Ehryk/GearDisplay/Documentation/PCB Routing/Shift Sensor Unit - v4.png

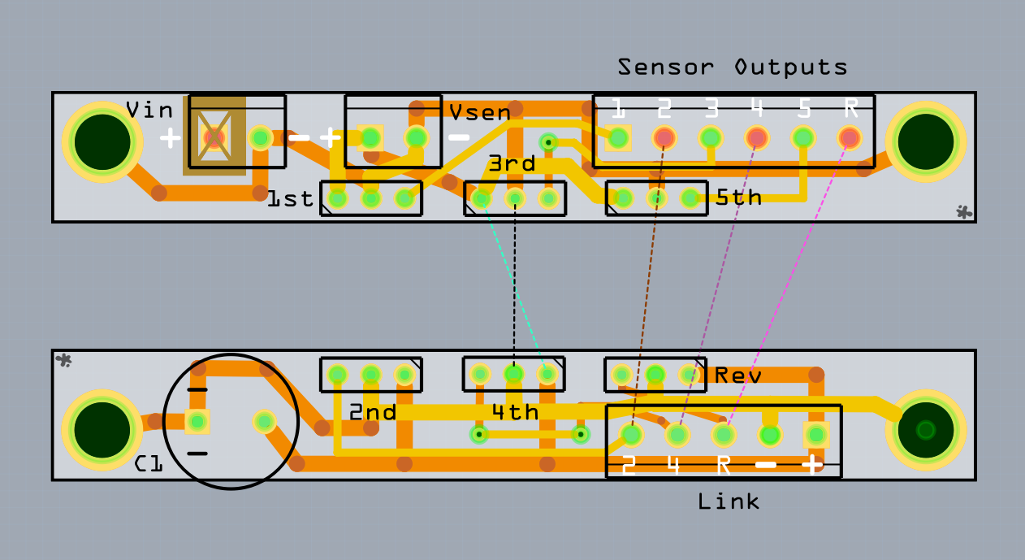
Documentation/PCB Routing/Shift Sensor Unit - v4.png
