Ehryk/GearDisplay/Documentation/Pictures/2013.01.10 - Breadboard/2 - Intro Credits.jpg

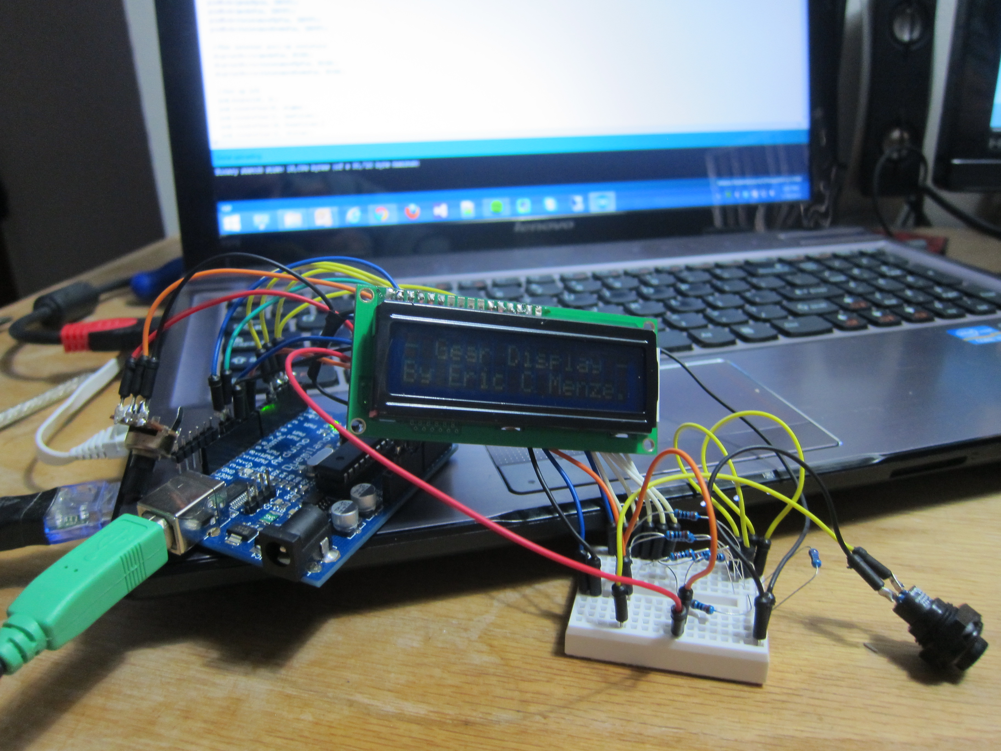
Documentation/Pictures/2013.01.10 - Breadboard/2 - Intro Credits.jpg
