Ehryk/GearDisplay/Documentation/Pictures/2013.01.10 - Breadboard/3 - Second Gear.jpg

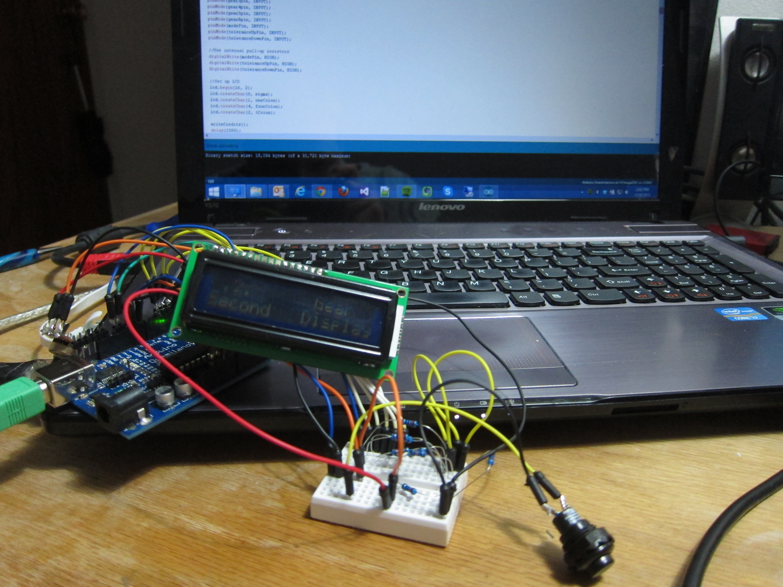
Documentation/Pictures/2013.01.10 - Breadboard/3 - Second Gear.jpg
