Ehryk/GearDisplay/Documentation/Pictures/2013.01.20 - Stripboard/1 - Basic Display.jpg

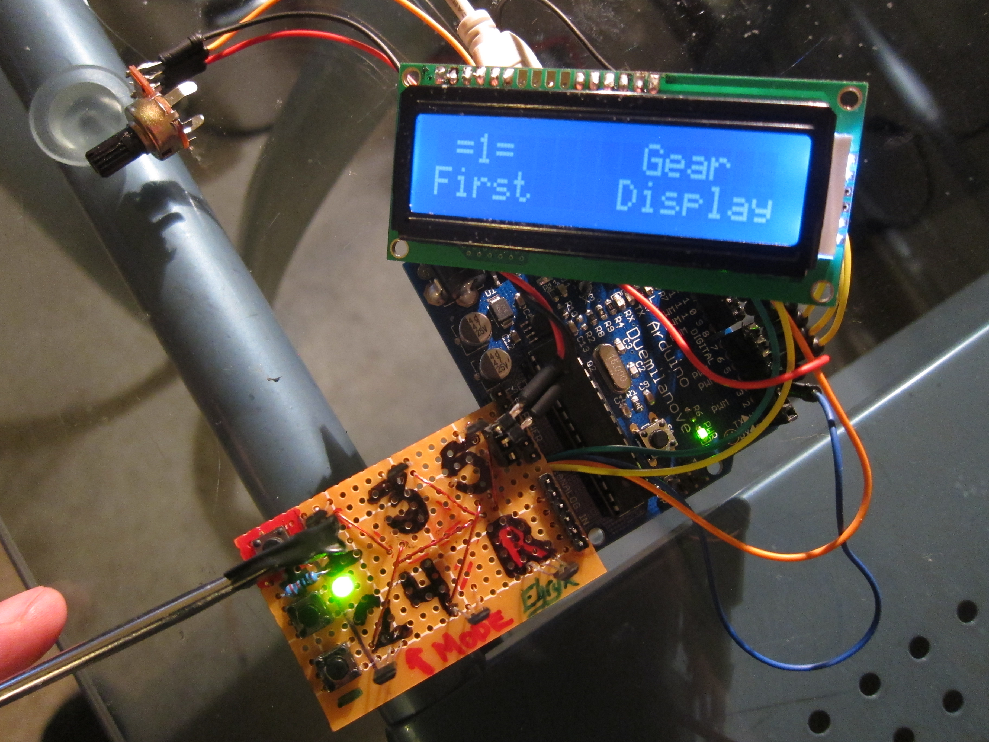
Documentation/Pictures/2013.01.20 - Stripboard/1 - Basic Display.jpg
