Ehryk/GearDisplay/Documentation/Pictures/2013.01.20 - Stripboard/4 - Voltage Display.jpg

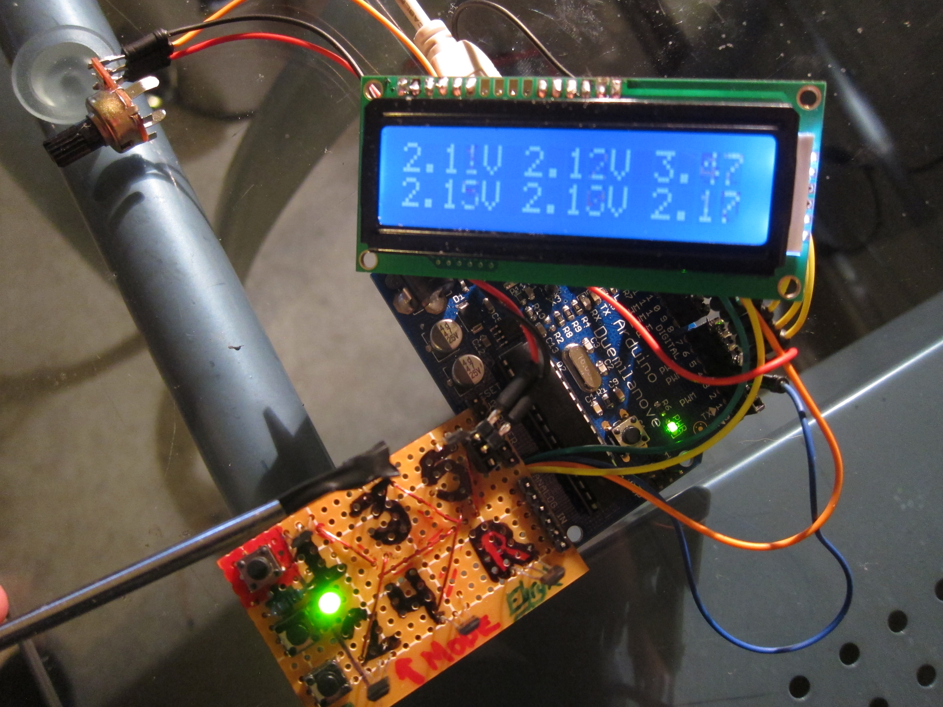
Documentation/Pictures/2013.01.20 - Stripboard/4 - Voltage Display.jpg
