Ehryk/GearDisplay/Documentation/Pictures/2013.01.20 - Stripboard/5 - Setting Brightness.jpg

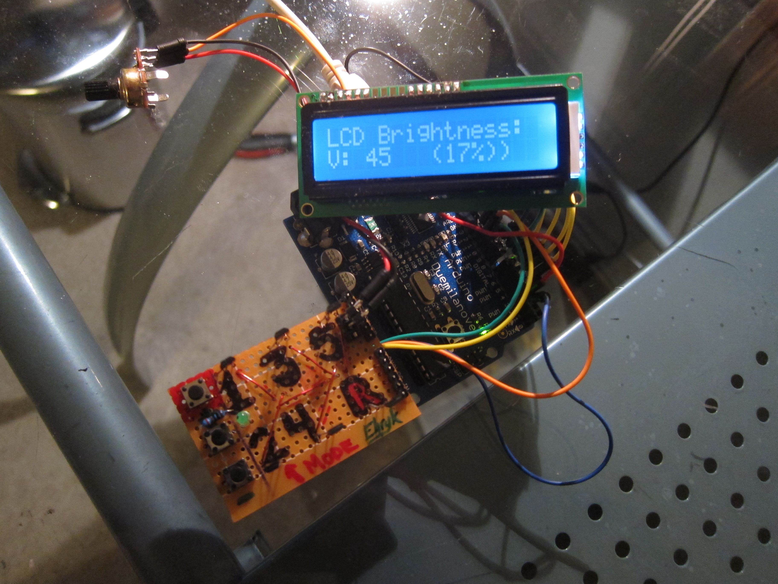
Documentation/Pictures/2013.01.20 - Stripboard/5 - Setting Brightness.jpg
