Ehryk/GearDisplay/Documentation/Pictures/2013.02.07 - Fritzing PCBs/1 - GearDisplay PCB Shield.JPG

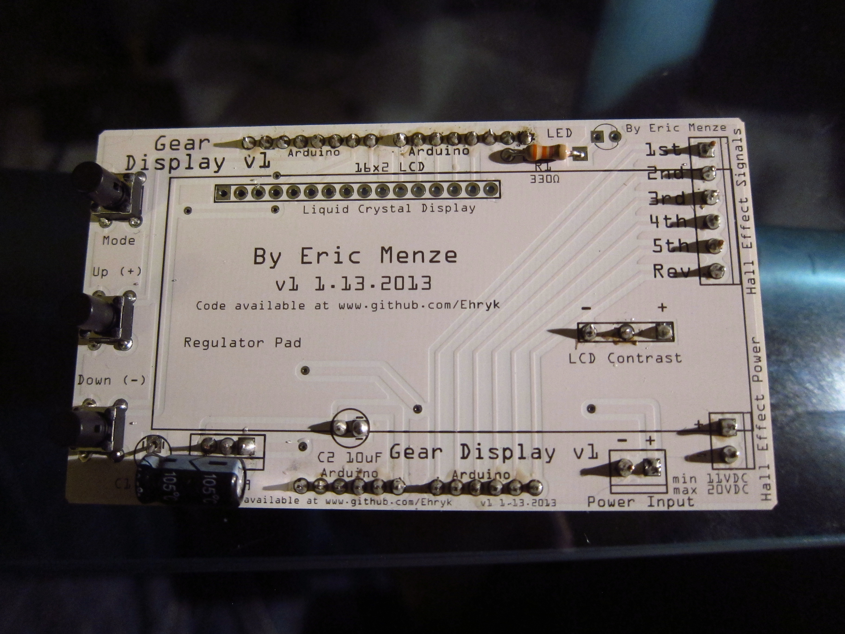
Documentation/Pictures/2013.02.07 - Fritzing PCBs/1 - GearDisplay PCB Shield.JPG
