Ehryk/GearDisplay/Documentation/Pictures/2013.02.07 - Fritzing PCBs/2 - Next to Arduino Uno.JPG

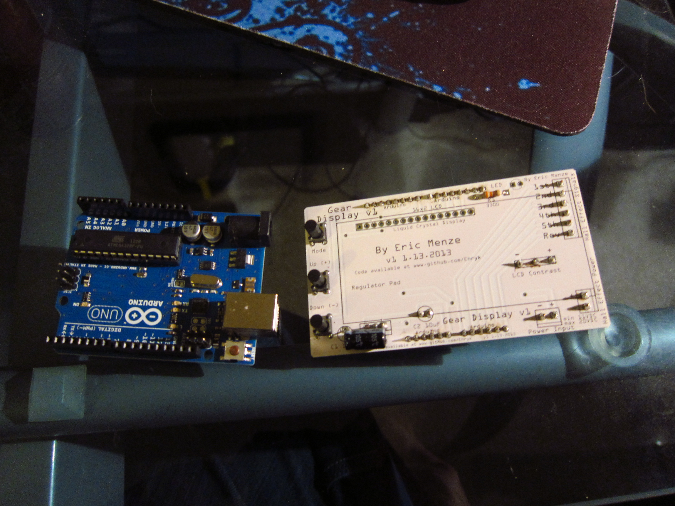
Documentation/Pictures/2013.02.07 - Fritzing PCBs/2 - Next to Arduino Uno.JPG
