Ehryk/GearDisplay/Documentation/Pictures/2013.02.07 - Fritzing PCBs/3 - Back of Board.JPG

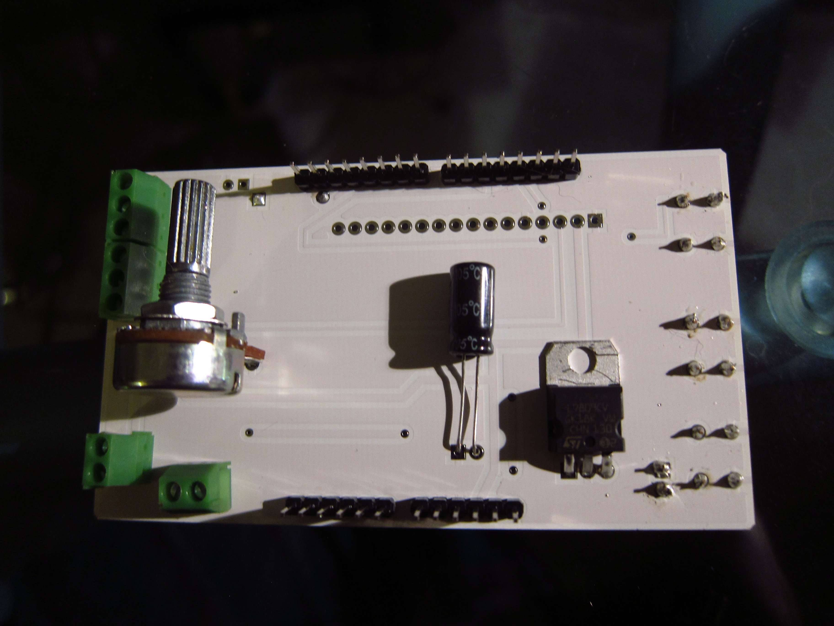
Documentation/Pictures/2013.02.07 - Fritzing PCBs/3 - Back of Board.JPG
