Ehryk/GearDisplay/Documentation/Pictures/2013.02.07 - Fritzing PCBs/4 - With LCD.JPG

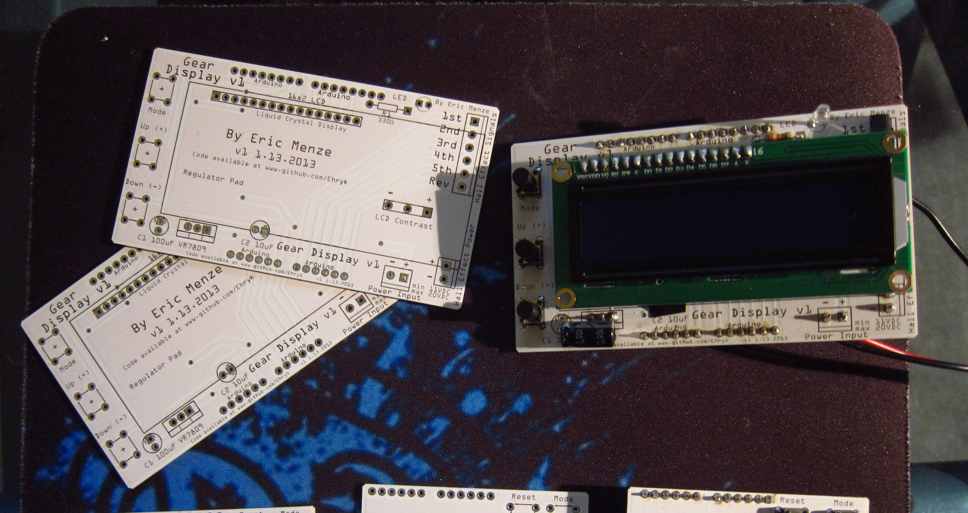
Documentation/Pictures/2013.02.07 - Fritzing PCBs/4 - With LCD.JPG
