Ehryk/GearDisplay/Documentation/Pictures/The Market.png

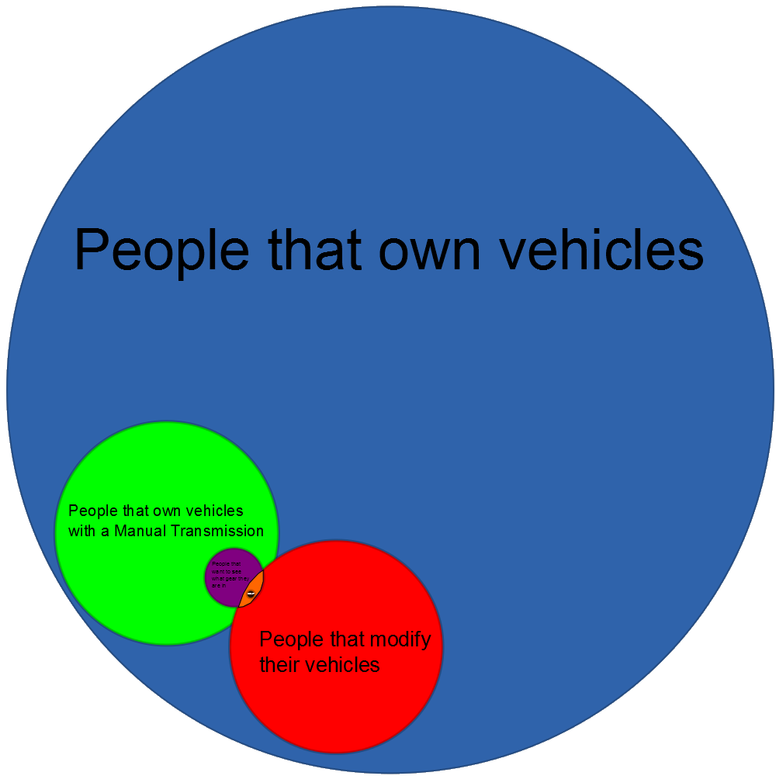
Documentation/Pictures/The Market.png
