Ehryk/GearDisplay/v1.0 - 16x2 LCD Display/PCB/GearDisplay PCB.png

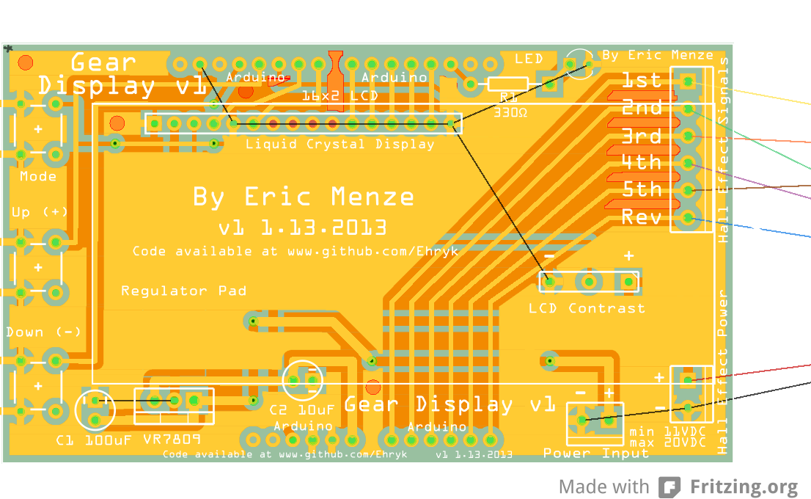
v1.0 - 16x2 LCD Display/PCB/GearDisplay PCB.png
