Ehryk/GearDisplay/v1.0 - 16x2 LCD Display/Pictures/1.10.2013/IMG_4925.JPG

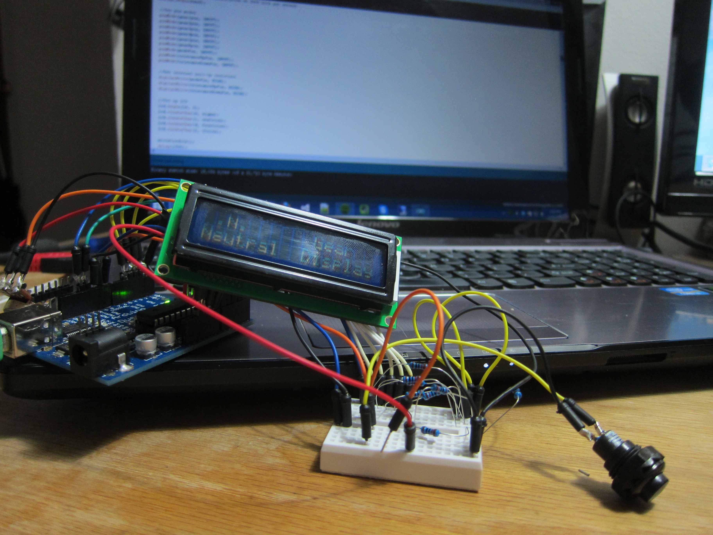
v1.0 - 16x2 LCD Display/Pictures/1.10.2013/IMG_4925.JPG
