Ehryk/GearDisplay/v1.0 - 16x2 LCD Display/Pictures/1.20.2013/IMG_5246.JPG

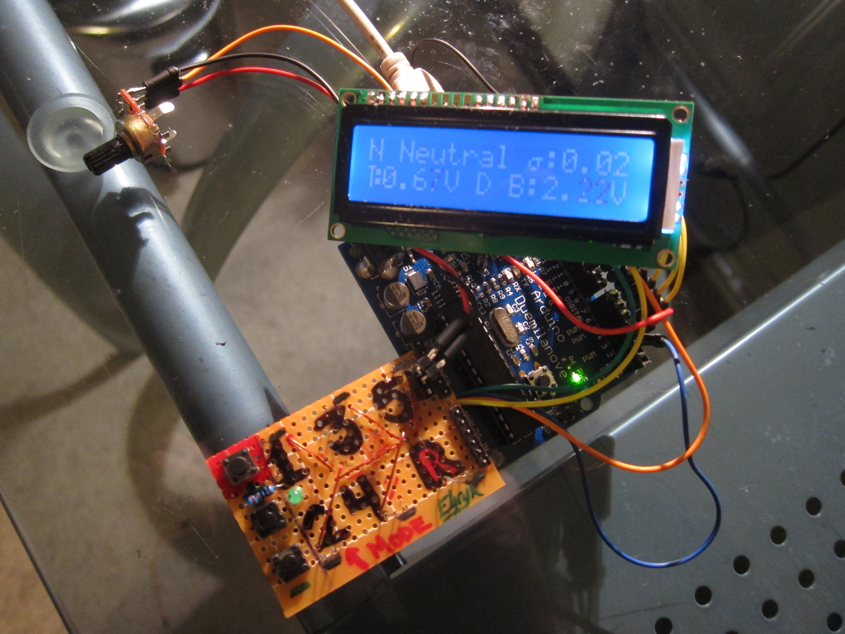
v1.0 - 16x2 LCD Display/Pictures/1.20.2013/IMG_5246.JPG
