Ehryk/GearDisplay/Documentation/Pictures/2013.09.06 - Install/1 - Prepping Arduino Uno.jpg

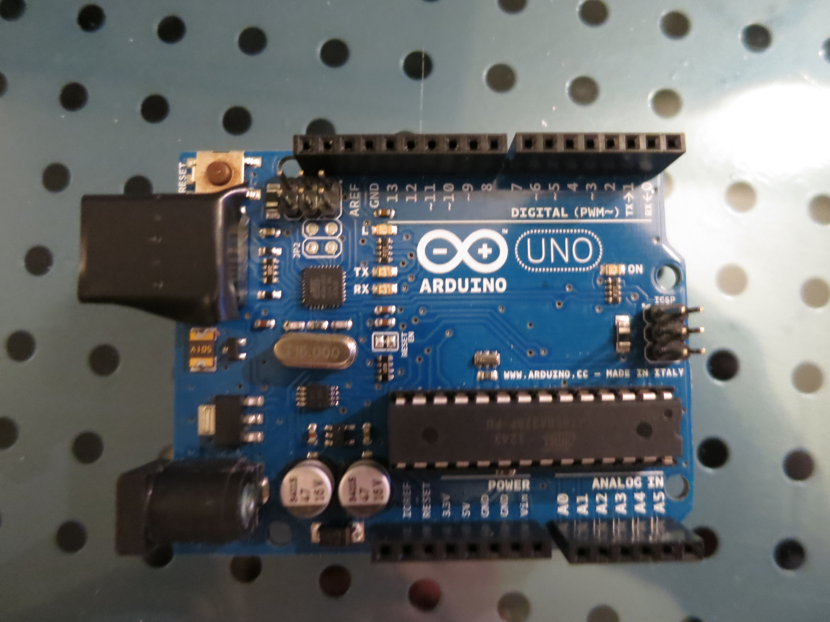
Documentation/Pictures/2013.09.06 - Install/1 - Prepping Arduino Uno.jpg
