Ehryk/GearDisplay/Documentation/Pictures/2013.09.06 - Install/2 - Soldering Ultracapacitor Keep-Alive.jpg

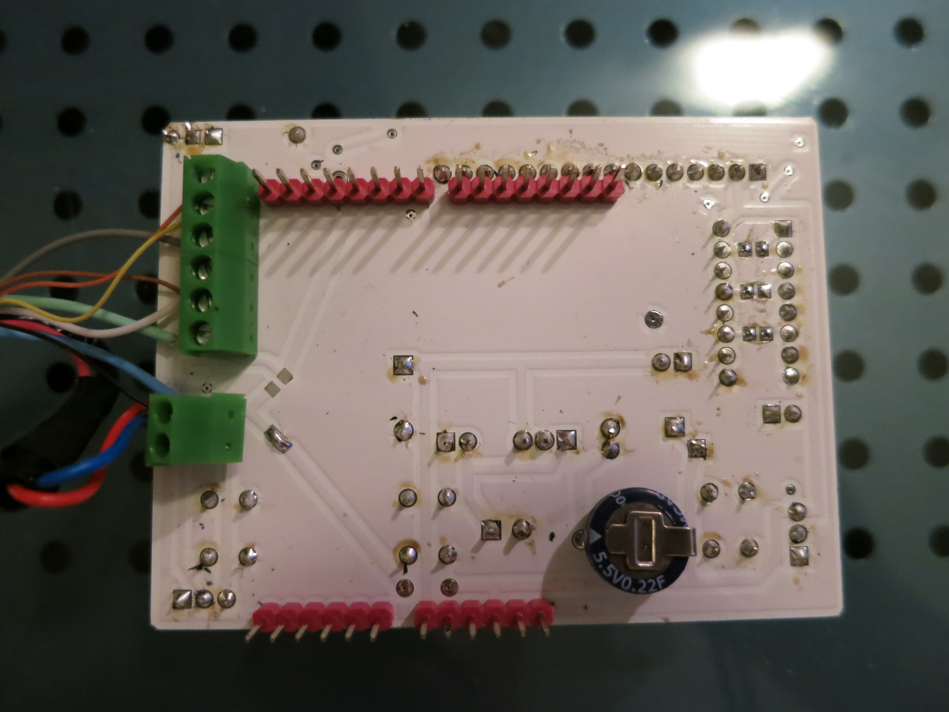
Documentation/Pictures/2013.09.06 - Install/2 - Soldering Ultracapacitor Keep-Alive.jpg
