Ehryk/GearDisplay/Documentation/Pictures/2013.09.06 - Install/5 - Hall Effect Installation.jpg

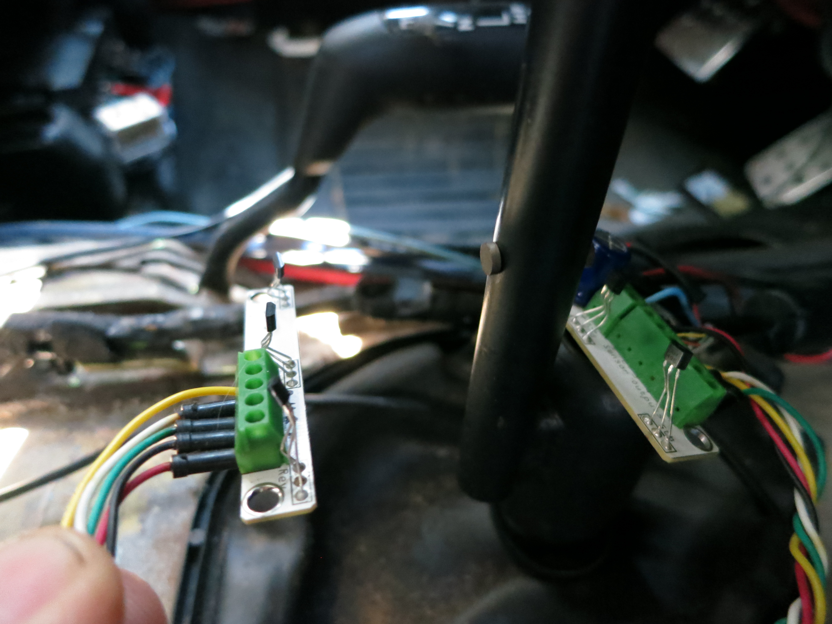
Documentation/Pictures/2013.09.06 - Install/5 - Hall Effect Installation.jpg
