Ehryk/GearDisplay/Documentation/Pictures/2013.09.06 - Install/6 - Mounting on Dashboard.jpg

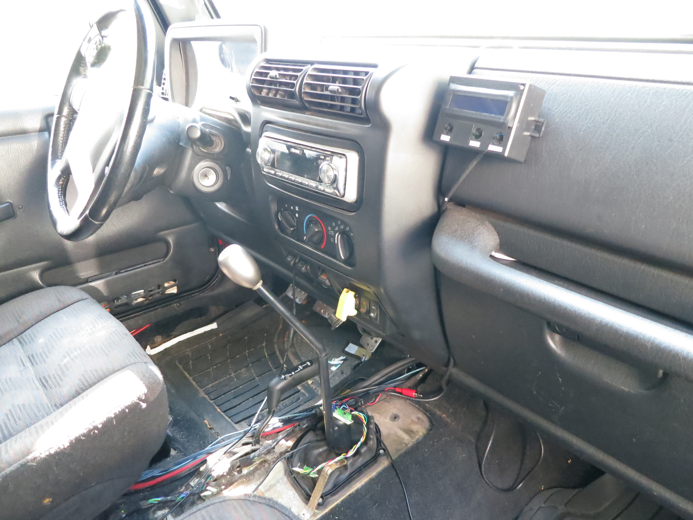
Documentation/Pictures/2013.09.06 - Install/6 - Mounting on Dashboard.jpg
