Ehryk/GearDisplay/Documentation/Pictures/2015.09.15 - Resolder Install/1 - Jeep Shifter Install.JPG

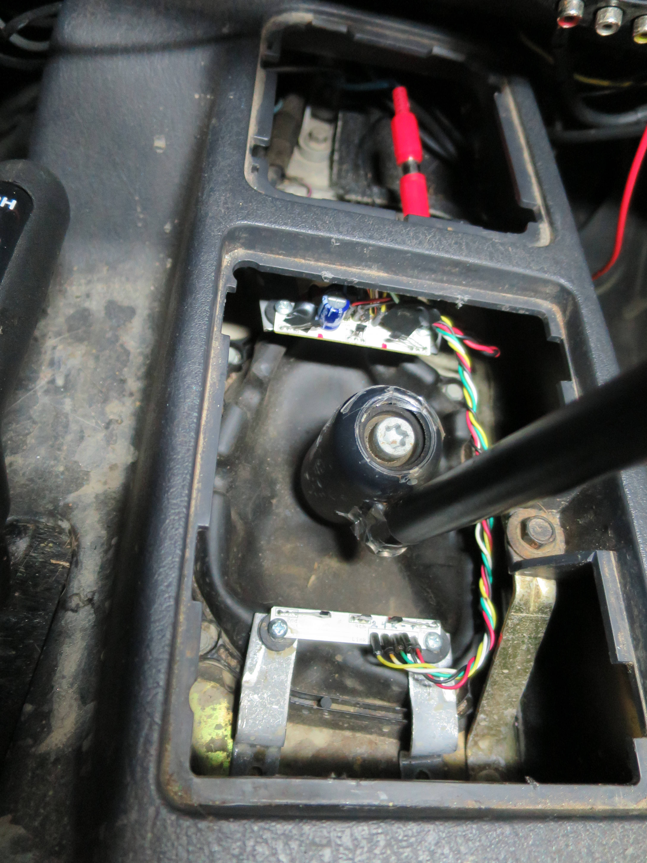
Documentation/Pictures/2015.09.15 - Resolder Install/1 - Jeep Shifter Install.JPG
