Ehryk/GearDisplay/Documentation/Pictures/2015.09.15 - Resolder Install/2 - Top Board (1,3,5).JPG

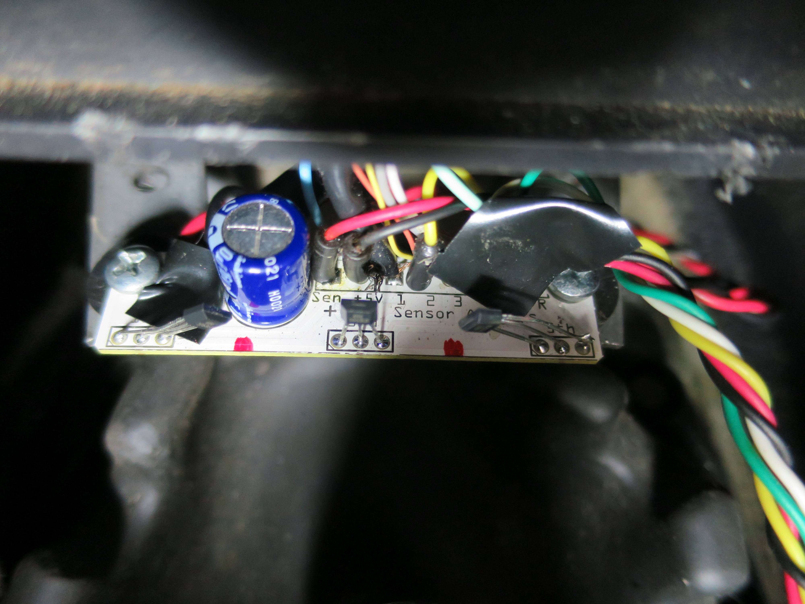
Documentation/Pictures/2015.09.15 - Resolder Install/2 - Top Board (1,3,5).JPG
