Ehryk/GearDisplay/Documentation/Pictures/2015.09.15 - Resolder Install/3 - Bottom Board (2, 4, R).JPG

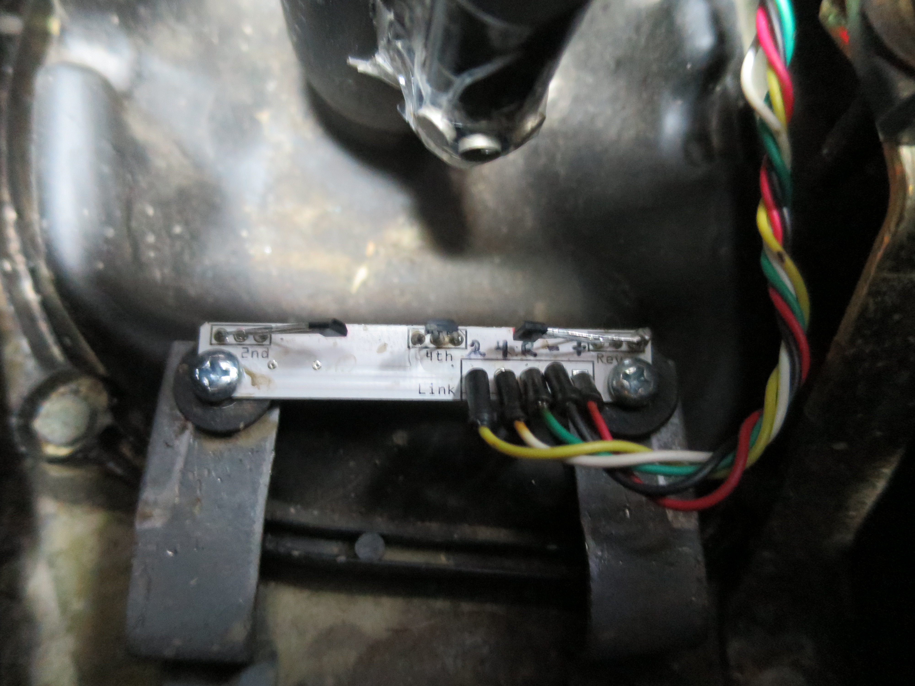
Documentation/Pictures/2015.09.15 - Resolder Install/3 - Bottom Board (2, 4, R).JPG
