Ehryk/GearDisplay/v2 - 16x2 LCD Display in Casing/PCB/PDF/Schematic v2 - With Bounce Eliminator_etch_silk_top.pdf

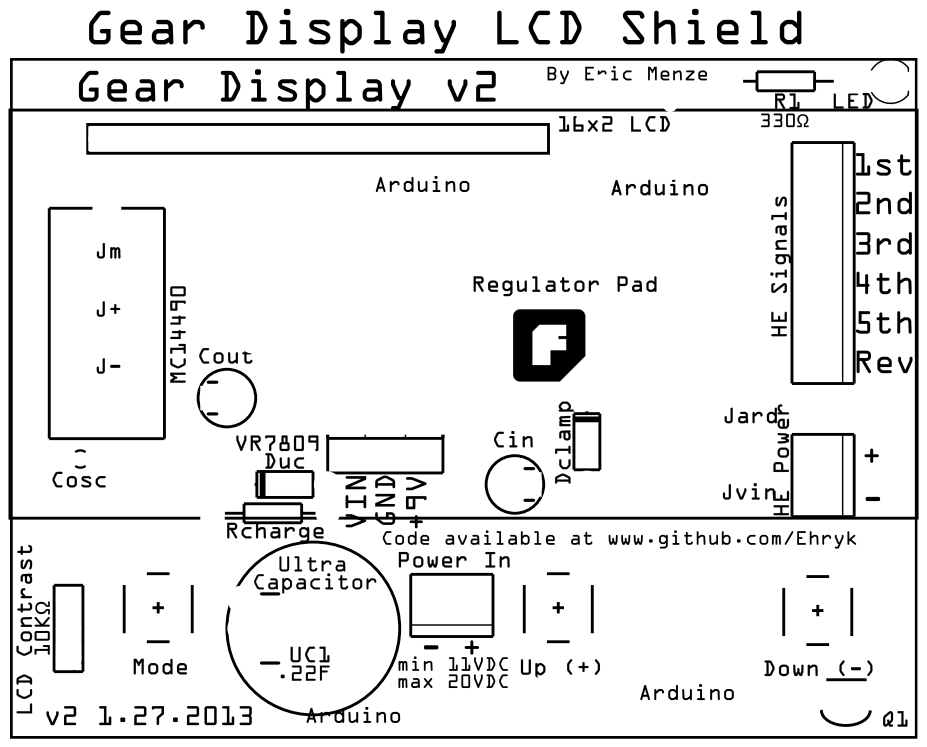
[picture p46: page 1]
