Ehryk/GearDisplay/v2 - 16x2 LCD Display in Casing/PCB/PDF/Schematic v2 - With Bounce Eliminator_etch_silk_top_mirror.pdf

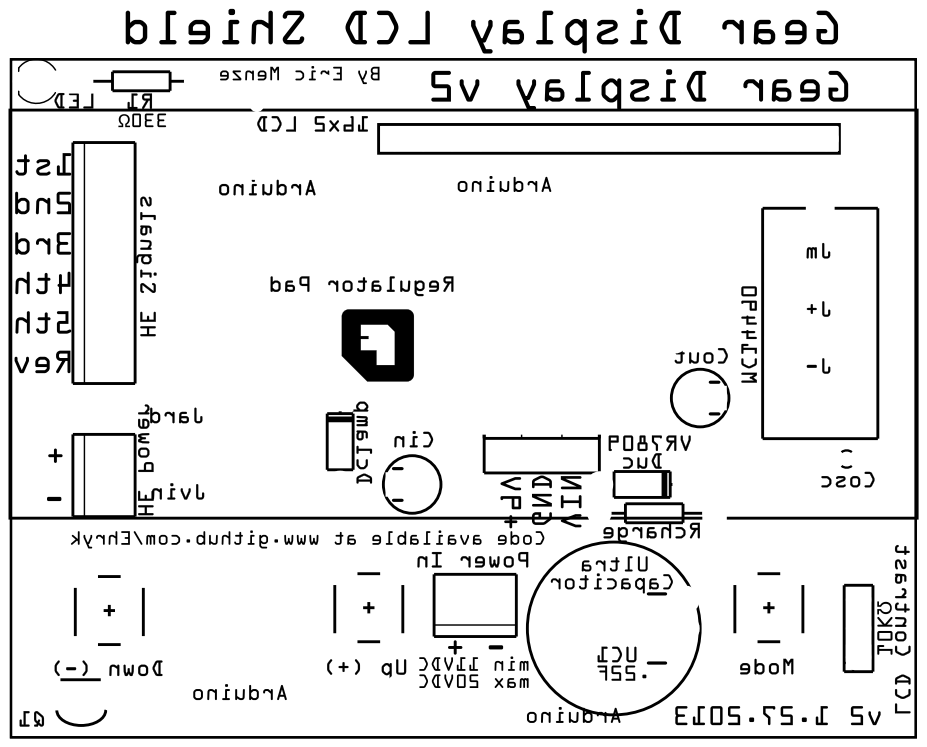
[picture p47: page 1]
