Ehryk/GearDisplay/Shift Sensor Unit/PCB/v2 - Open Rectangle/Schematic v2 - Open Ring_etch_copper_bottom.pdf

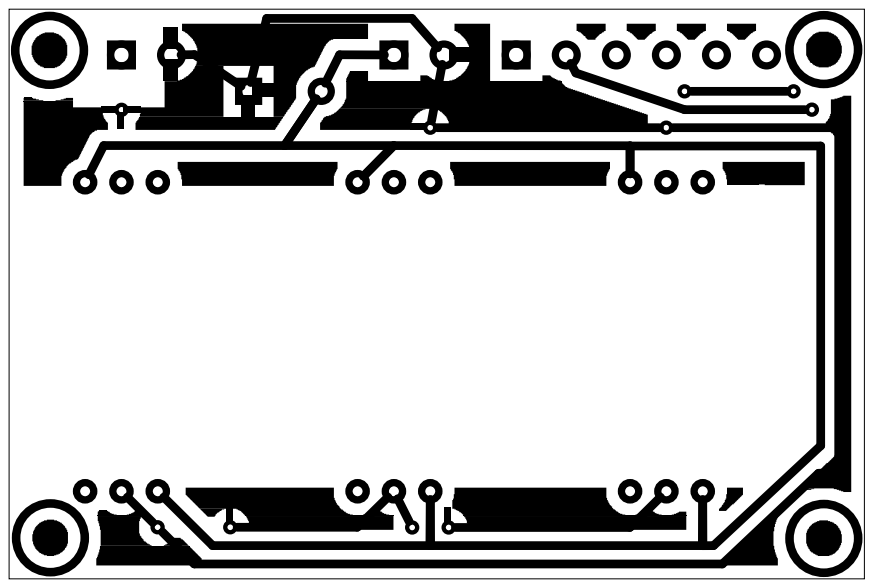
[picture p48: page 1]
