Ehryk/GearDisplay/Shift Sensor Unit/PCB/v2 - Open Rectangle/Schematic v2 - Open Ring_etch_copper_bottom_mirror.pdf

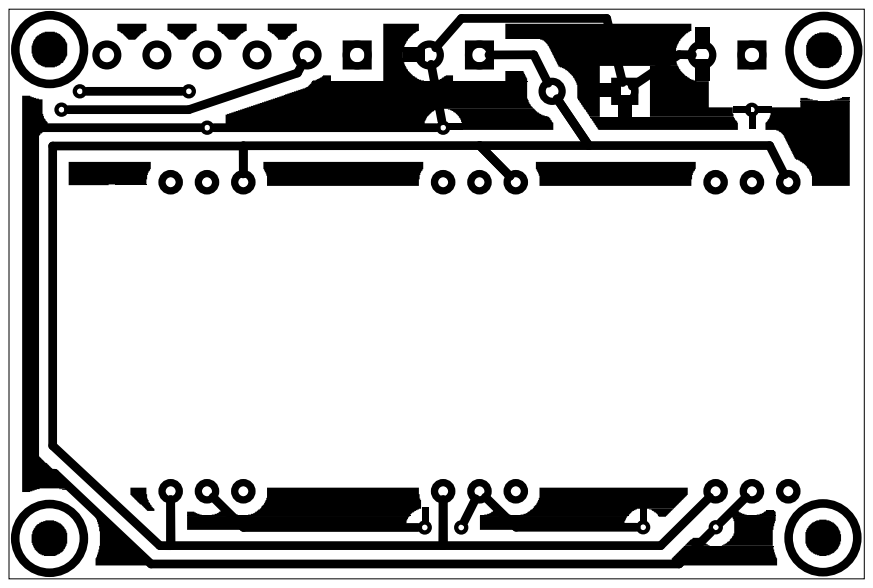
[picture p49: page 1]
