Ehryk/GearDisplay/Shift Sensor Unit/PCB/v2 - Open Rectangle/Schematic v2 - Open Ring_etch_copper_top.pdf

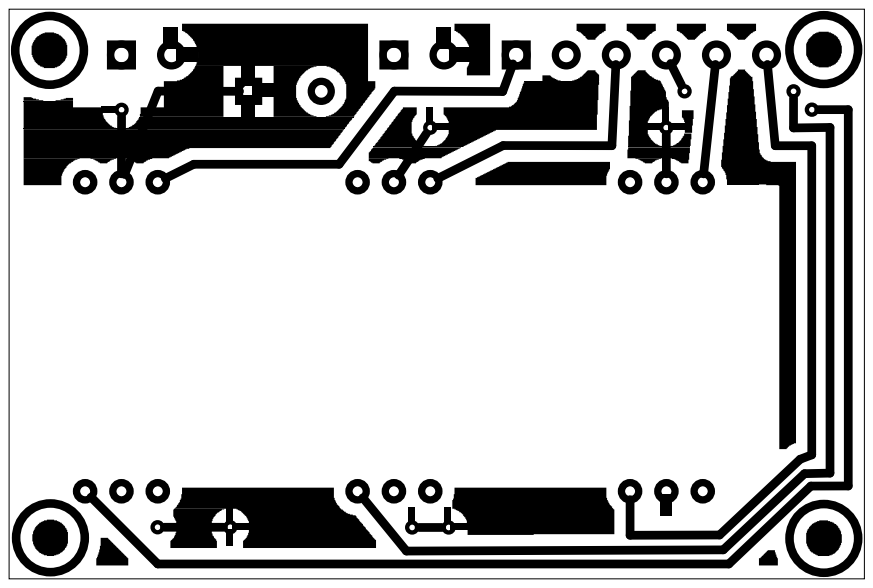
[picture p50: page 1]
