Ehryk/GearDisplay/Shift Sensor Unit/PCB/v2 - Open Rectangle/Schematic v2 - Open Ring_etch_mask_bottom.pdf

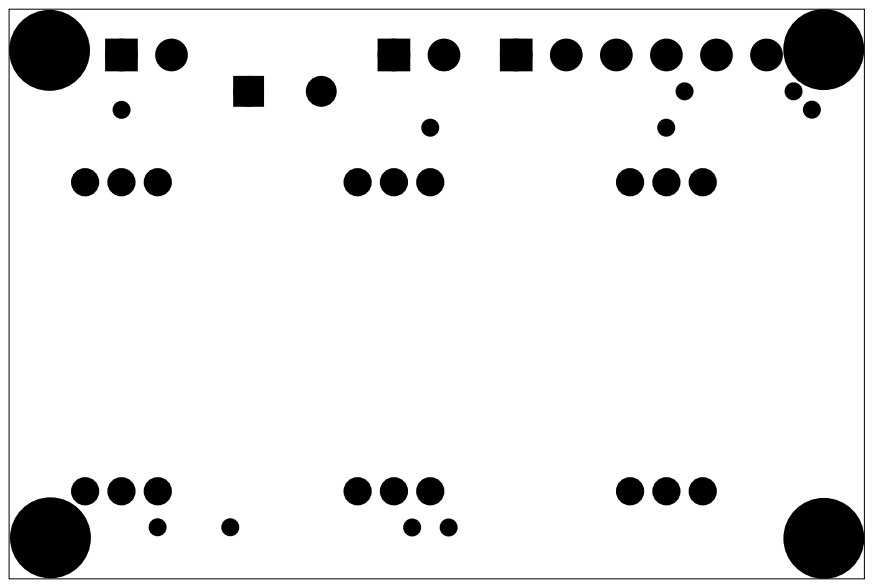
[picture p52: page 1]
