Ehryk/GearDisplay/Shift Sensor Unit/PCB/v2 - Open Rectangle/Schematic v2 - Open Ring_etch_mask_bottom_mirror.pdf

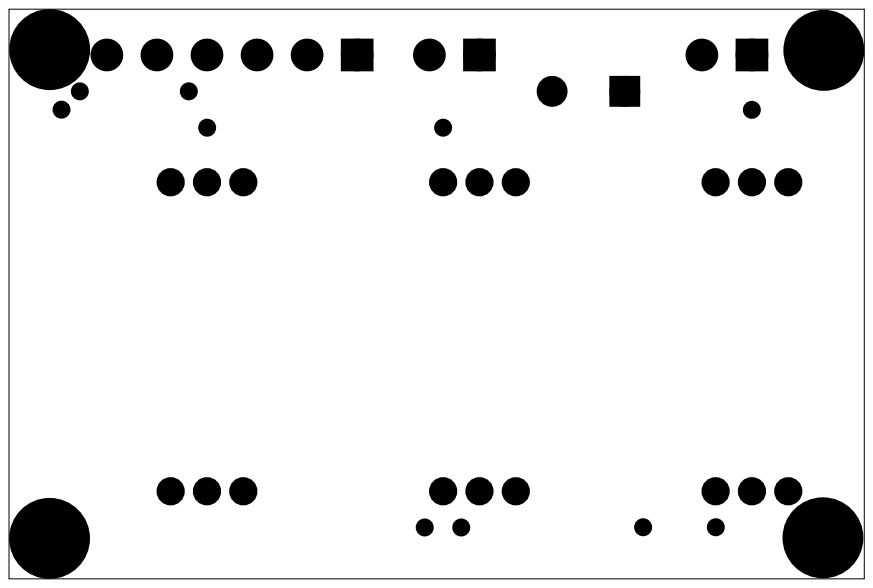
[picture p53: page 1]
