Ehryk/GearDisplay/Shift Sensor Unit/PCB/v2 - Open Rectangle/Schematic v2 - Open Ring_etch_silk_top_mirror.pdf

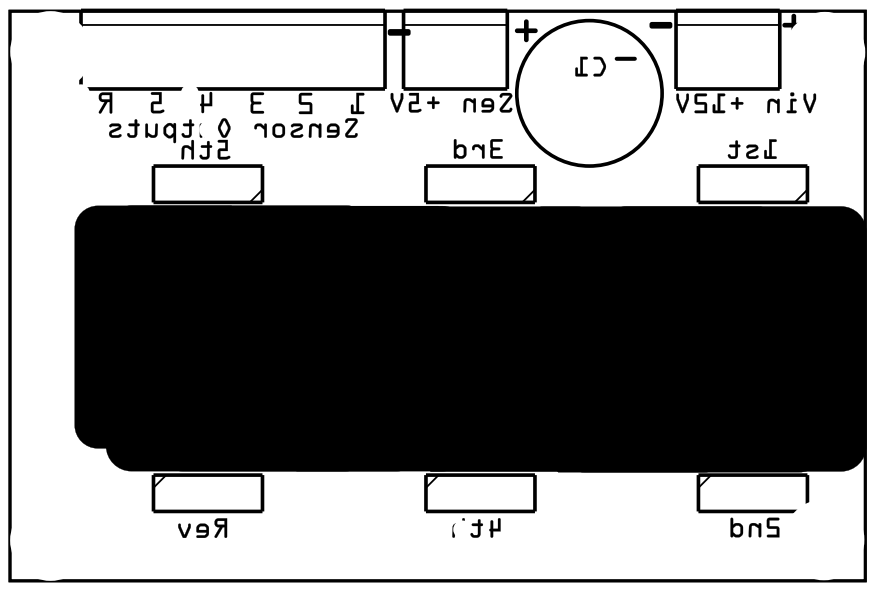
[picture p55: page 1]
