Ehryk/GearDisplay/Shift Sensor Unit/PCB/v1 - Closed Rectangle/Schematic_etch_copper_bottom.pdf

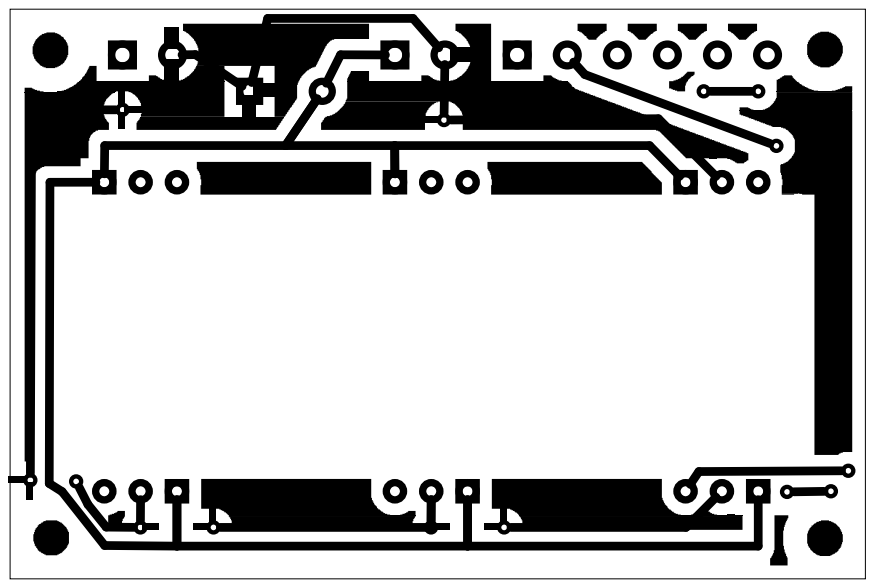
[picture p56: page 1]
