Ehryk/GearDisplay/Shift Sensor Unit/PCB/v1 - Closed Rectangle/Schematic_etch_copper_bottom_mirror.pdf

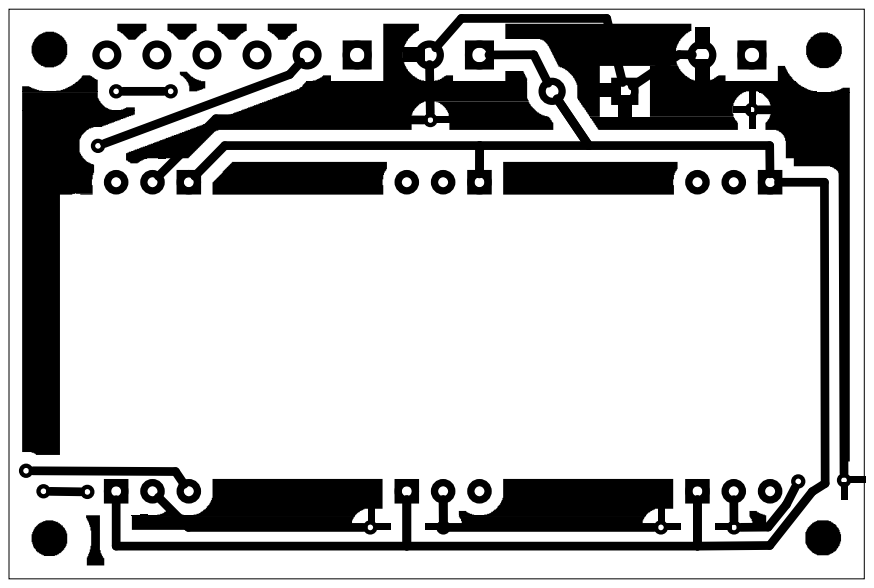
[picture p57: page 1]
