Ehryk/GearDisplay/Shift Sensor Unit/PCB/v1 - Closed Rectangle/Schematic_etch_copper_top.pdf

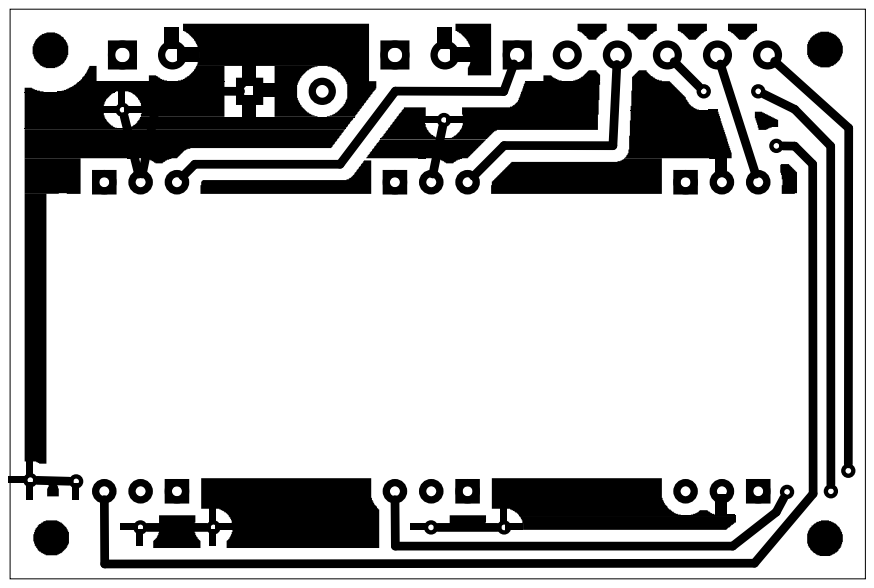
[picture p58: page 1]
