Ehryk/GearDisplay/Shift Sensor Unit/PCB/v1 - Closed Rectangle/Schematic_etch_copper_top_mirror.pdf

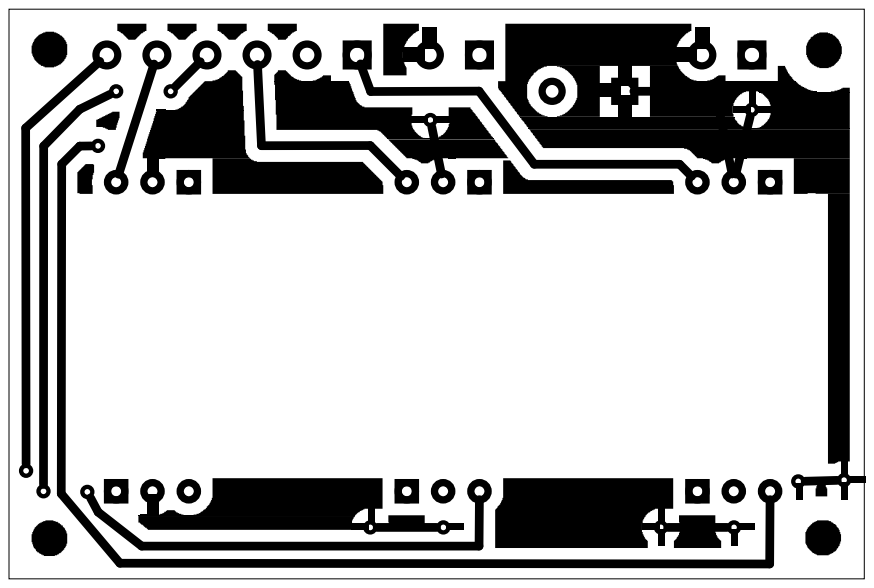
[picture p59: page 1]
