Ehryk/GearDisplay/Shift Sensor Unit/PCB/v1 - Closed Rectangle/Schematic_etch_mask_bottom.pdf

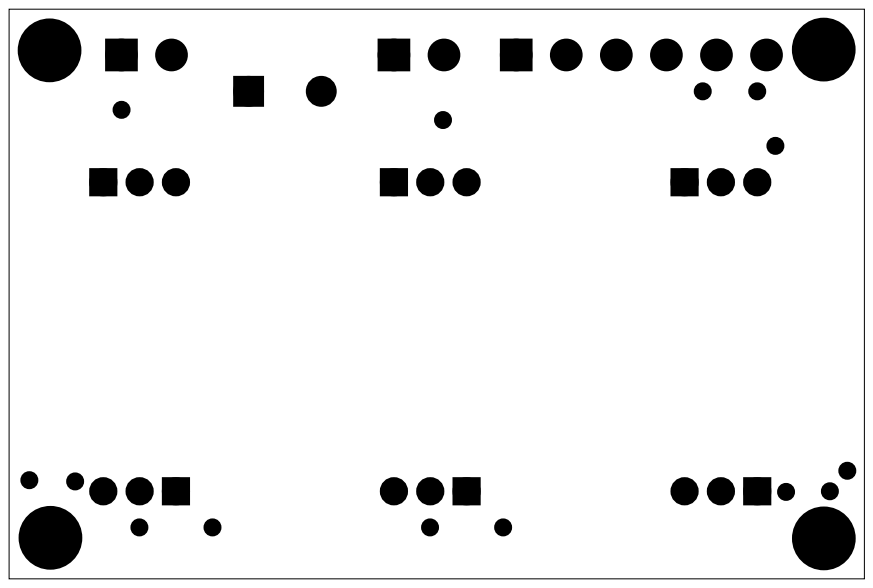
[picture p60: page 1]
