Ehryk/GearDisplay/Shift Sensor Unit/PCB/v1 - Closed Rectangle/Schematic_etch_mask_bottom_mirror.pdf

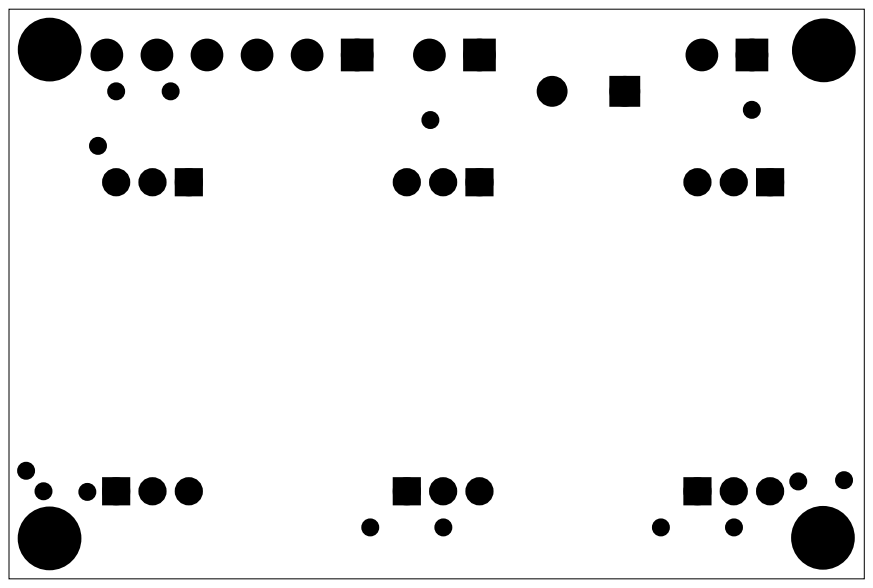
[picture p61: page 1]
