Ehryk/GearDisplay/Shift Sensor Unit/PCB/v1 - Closed Rectangle/Schematic_etch_silk_top_mirror.pdf

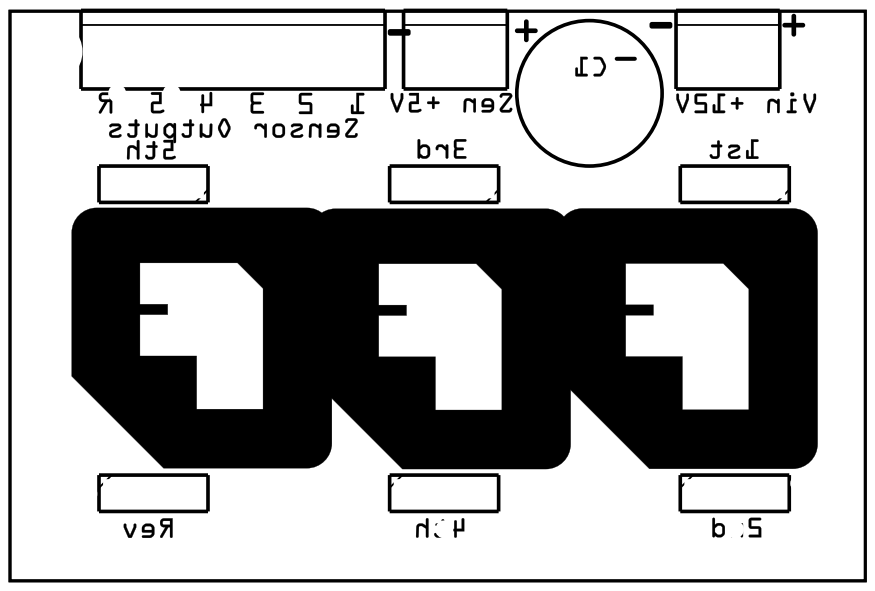
[picture p63: page 1]
